ioannis-0/Guitar-Amplifier/Final personal project/guitar_amp_proj/guitar_amp/g_amp/g_amp.asc

C1: cap; 100n
R1: res; 91k
R2: res; 10k
R3: res; 1000k
U1: opamp2; tl072
U2: opamp2; tl072
V1: voltage; 12V
V2: voltage; -12V
V3: voltage; SINE(0 1m 50)
Named nets: 0, VCC+, VCC-
.include tl072.lib
.tran 0.5
